jdenavascues/Drosben/docs/img/colour_combos.png

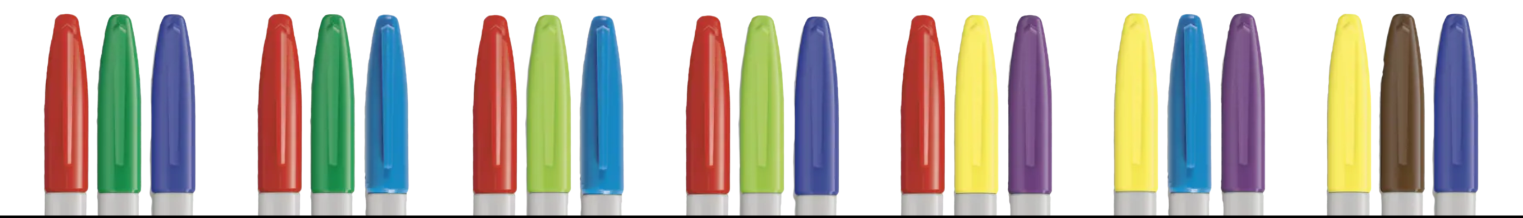
docs/img/colour_combos.png
