jdenavascues/Drosben/docs/img/colourmarkers_expanded.png

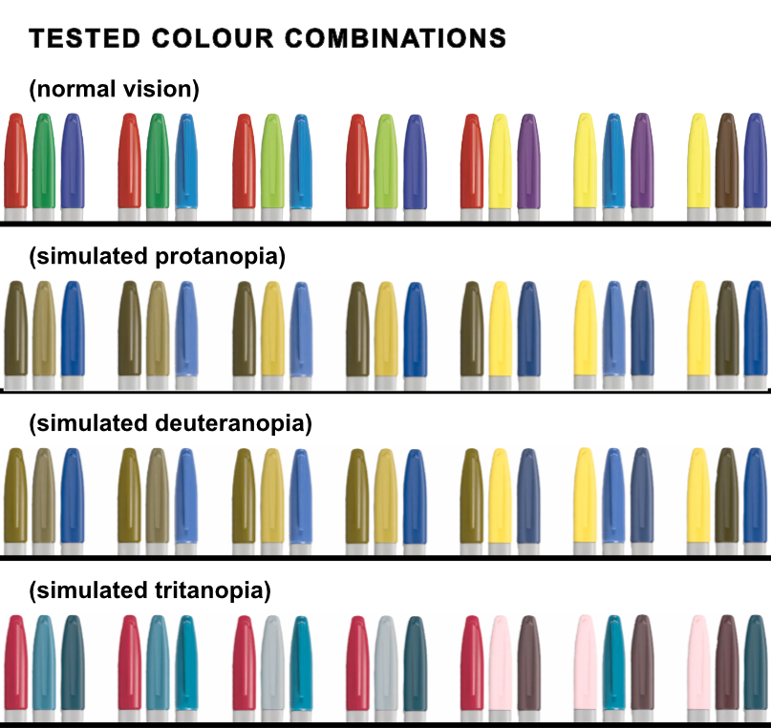
docs/img/colourmarkers_expanded.png
