jdenavascues/Drosben/docs/img/data_recording.png

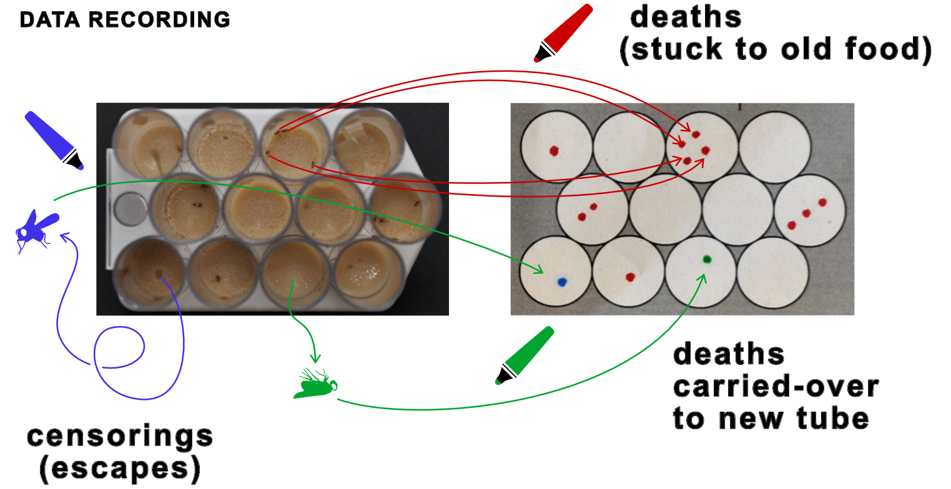
docs/img/data_recording.png
