jdenavascues/Drosben/docs/img/datasheet_header.png

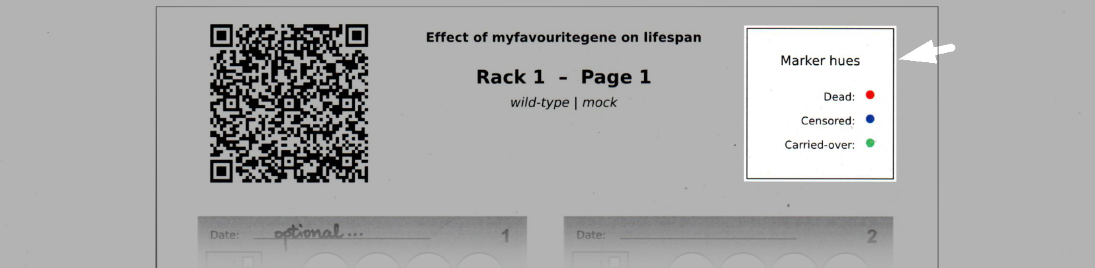
docs/img/datasheet_header.png
