jdenavascues/Drosben/docs/img/tube_numbering2.png

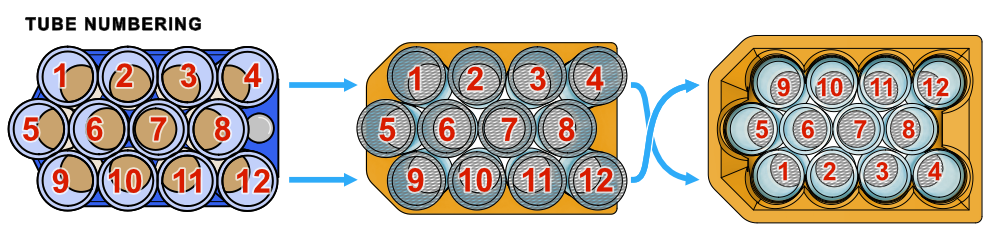
docs/img/tube_numbering2.png
