jdenavascues/Drosben/tests/data/datasheet_scans/r1p1.jpg

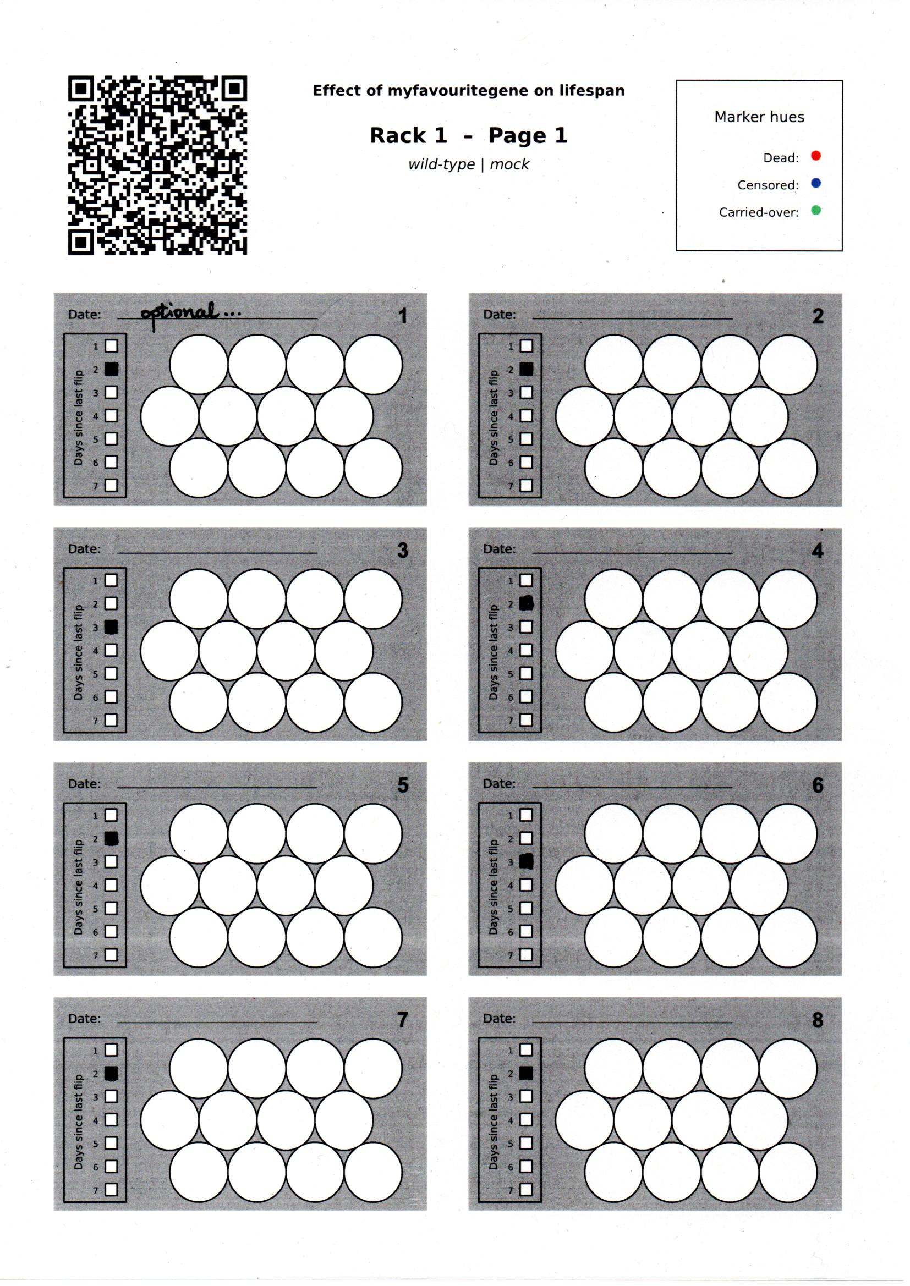
tests/data/datasheet_scans/r1p1.jpg
