jdenavascues/Drosben/tests/data/datasheet_scans/r1p3.jpg

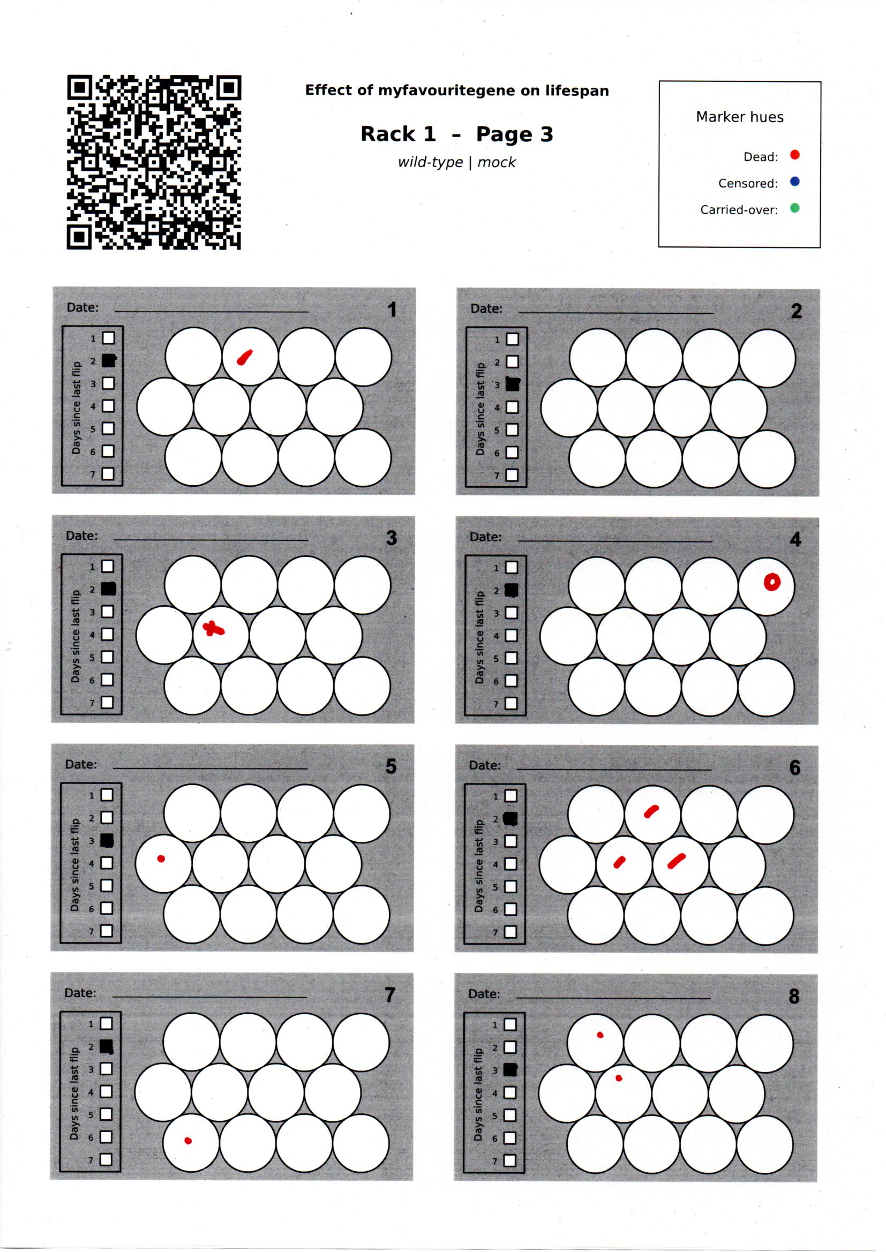
tests/data/datasheet_scans/r1p3.jpg
