jdenavascues/Drosben/tests/data/datasheet_scans/r2p2.jpg

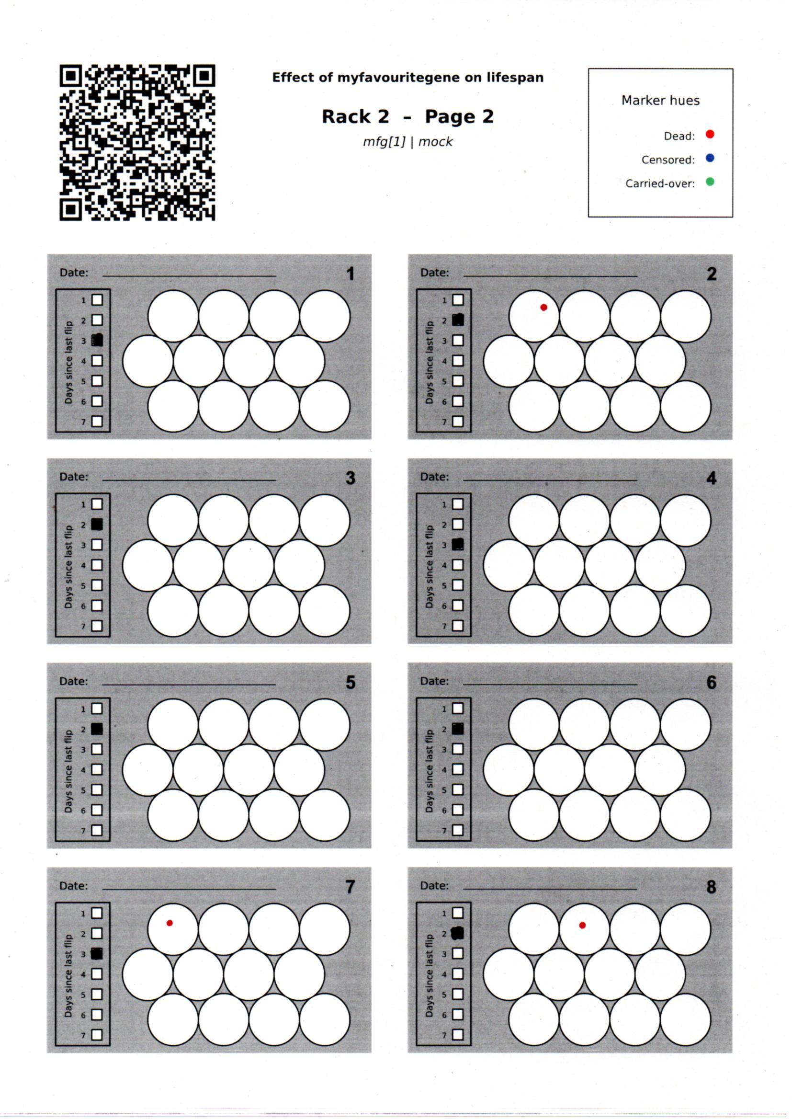
tests/data/datasheet_scans/r2p2.jpg
