jdenavascues/Drosben/tests/data/datasheet_scans/r4p4.jpg

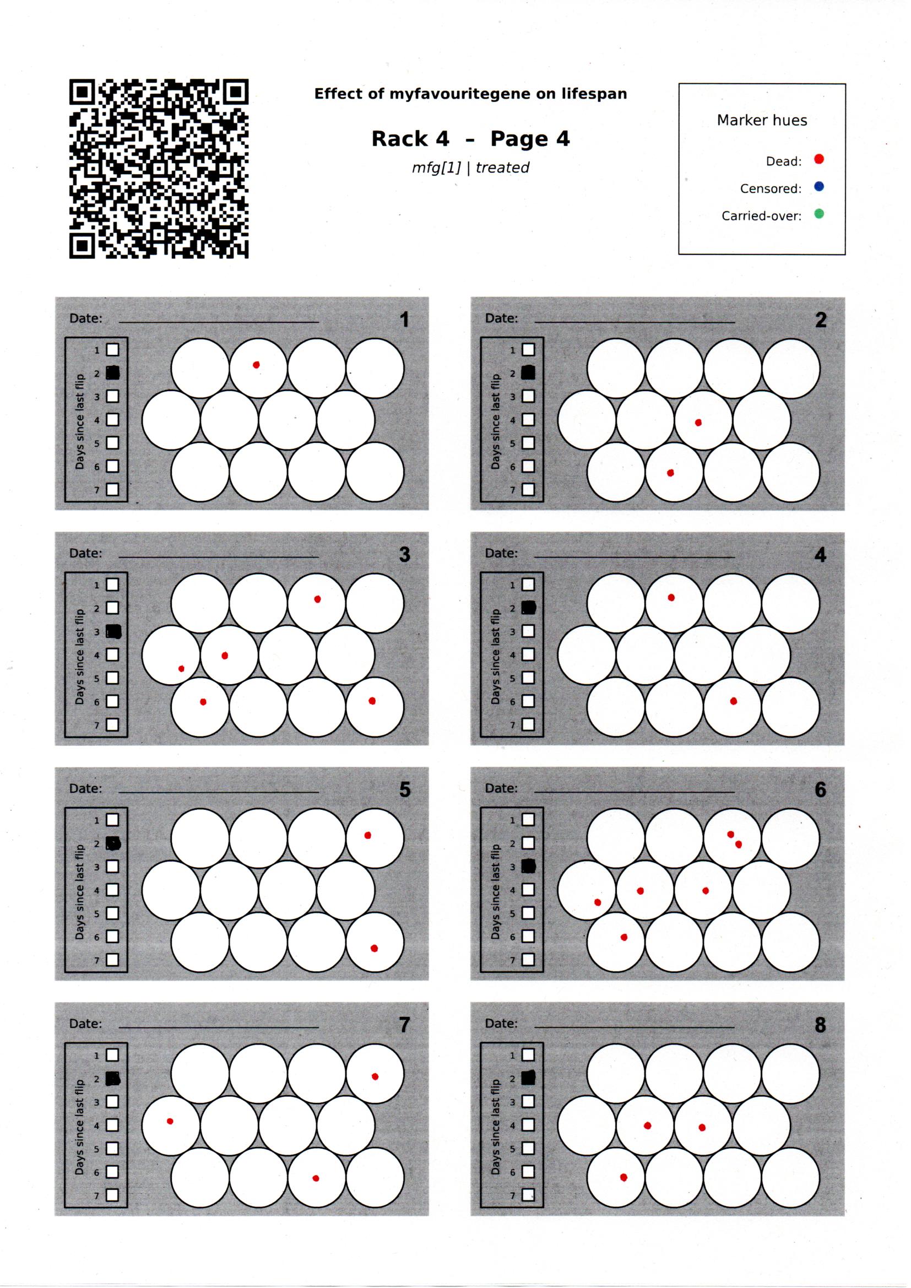
tests/data/datasheet_scans/r4p4.jpg
